fmetivier/LoggerPluvio/figures/20241003_105648.jpg

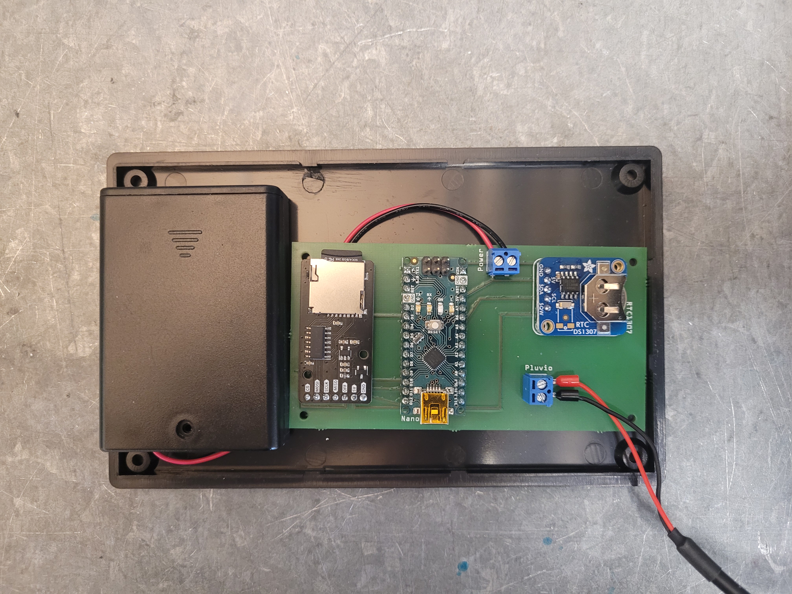
figures/20241003_105648.jpg
